jeffgregx2/ESPHomeCN105/images/WF-1/PCB-photo-HS.jpg

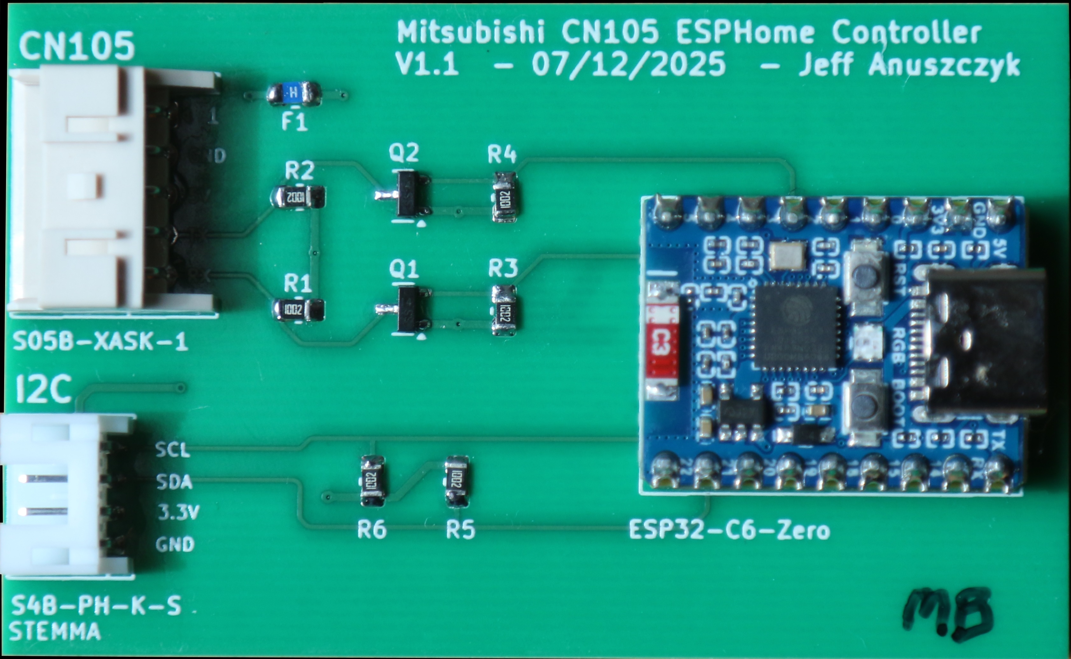
images/WF-1/PCB-photo-HS.jpg
