jeffgregx2/ESPHomeCN105/images/WF-1/PCB-V1.2-layout.png

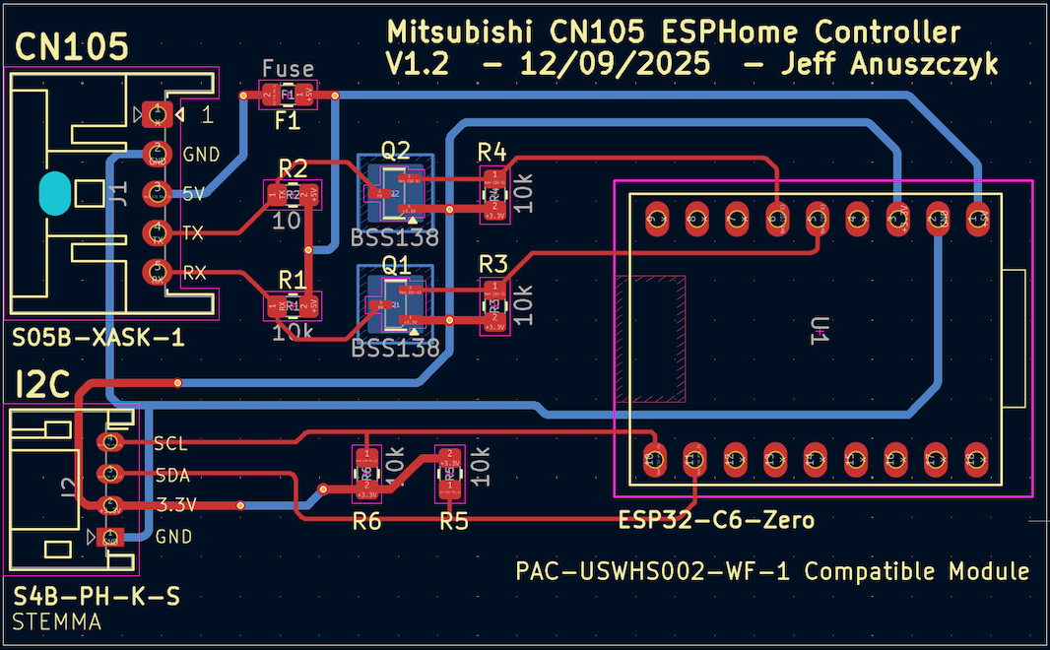
images/WF-1/PCB-V1.2-layout.png
